Machine-Hum/BirdEar/birdEar/img/be.jpg

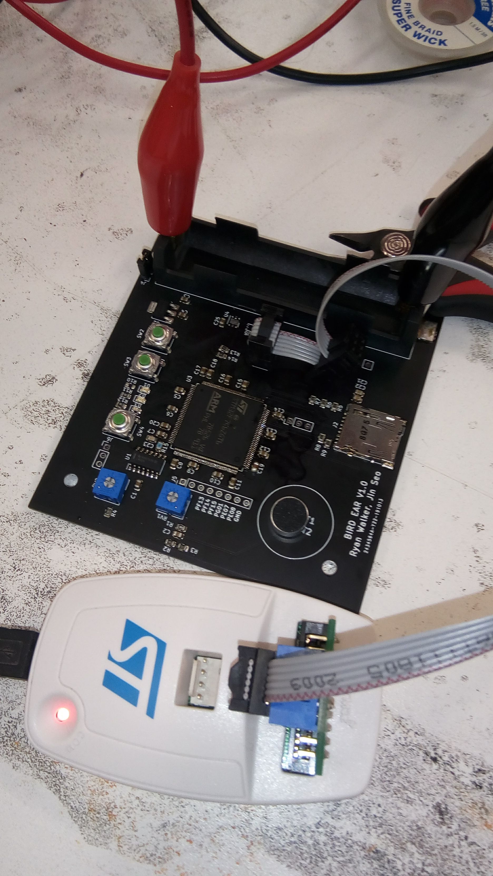
birdEar/img/be.jpg
