Machine-Hum/BirdEar/report/img/sigmoid2.png

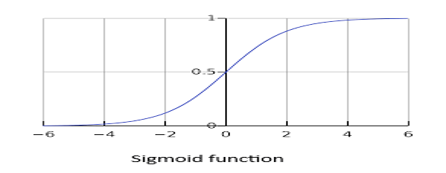
report/img/sigmoid2.png
